martin-dold/smartMug/Organization/SequenceDiagram/IMG_9756.JPG

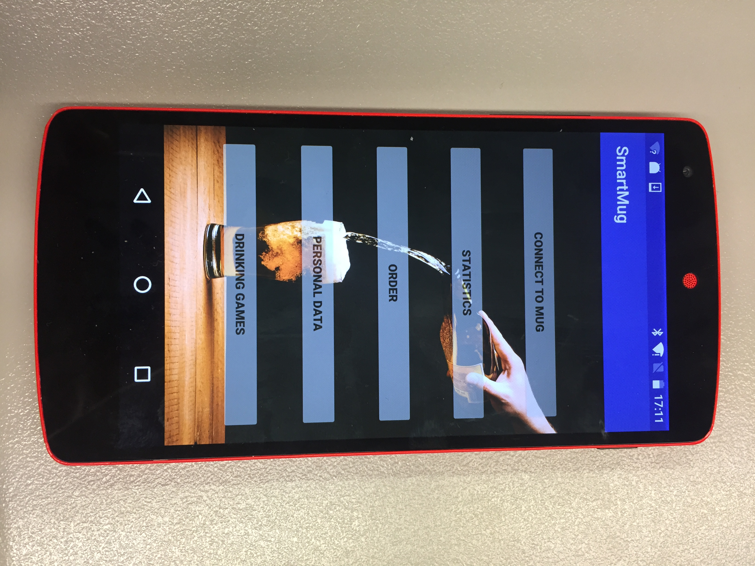
Organization/SequenceDiagram/IMG_9756.JPG
