martin-dold/smartMug/Organization/SequenceDiagram/IMG_20170131_155303.jpg

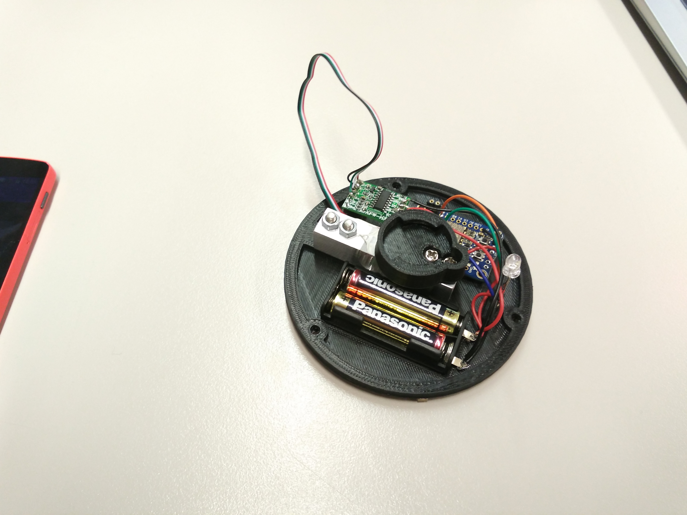
Organization/SequenceDiagram/IMG_20170131_155303.jpg
