martin-dold/smartMug/development/src/microcontroller/arduino/smartmug/serial.ino

/*! @file  serial.ino
 *  @brief This is the serial sketch of the smartmug project.
 *
 *  @defgroup serial Serial
 *  @brief Adds serial UART functionality to the smartmug.
 *
 *  @addtogroup arduino
 *  @{
 *
 *  @addtogroup serial
 *  @{
 */

/*! @brief Defines serial (UART) baudrate. */
#define BAUDRATE  115200


/*!
 * @brief Setup function of this ino sketch to setup serial port for operation.
 * @attention The serial port is initialized only if @ref DEBUG is enabled.
 */
void serial_setup()
{
  /* Serial is required for debugging only. */
#ifdef DEBUG
  Serial.begin(BAUDRATE);

  // Wait for serial port to connect. Needed for Leonardo only
  while (!Serial) { ; }
#endif

  DEBUG_PRINTLN("");
  DEBUG_PRINTLN("Serial connection ready.");
  DEBUG_PRINTLN("");
}

/*!
 * @}
 * @}
 */
